wayneandlayne/BluetoothArcadeController/pcb/v1.03/kicad/bluetooth_arcade_controller.sch

## KiCad design pcb/v1.03/kicad/bluetooth_arcade_controller.sch (2011-10-03)

Schematic: bluetooth_arcade_controller.sch

Parts:
C1, C2: 10u
C3: 100n
C4: 10p
D1, D2, D3, D4: LED
L1: 10 nH
P1, P2, P3, P4, P5, P6, P7, P8, P9, P10, P11, P12, P13, P14, P15, P16, P17, P18, P19, P20, P21, P22, P23, P24, P25, P26, P27, P28, P29, P30, P31, P32, P33, P34, P35, P36, P37, P38, P39, P40, P41, P42, P43, P44, P45, P46, P47, P48, P49, P50, P51, P52, P53, P54, P55, P56, P57, P58, P59, P60, P61, P62, P63, P64, P65, P66, P68, P69, P70, P71, P72, P73, P76, P77, P78, P79, P80, P81, P82, P83, P84, P85, P86, P87, P88, P89, P90, P91, P92, P93, P94, P95, P96, P97, P98, P99, P100: CONN_1
P67: CD
P74: ESC
P75: UART
R1, R2, R3, R4, R5, R6: 10k
R7, R8, R9, R10: R
SW1: PAIR
SW2: RESET
U1: WT12-A-VISUAL; sf-bluegiga-WT12-A
U2: MCP1825S
X1: ARDUINOSHIELDMEGA

Notes on the sheet:
Mounting holes, drill = 0.125, pad >= 0.145
LED0
LED1
WT12 CD
WT12 escape
Serial1
WT12 reset
Button Inputs
Pair Button
Serial
LED Outputs
TXD
